rana-sylvatica/rana-tadpole/PCBs/Motherboard/KiCAD files/qw-footprints/qw-footprints/RP2040_QFN_PACKAGE.STEP

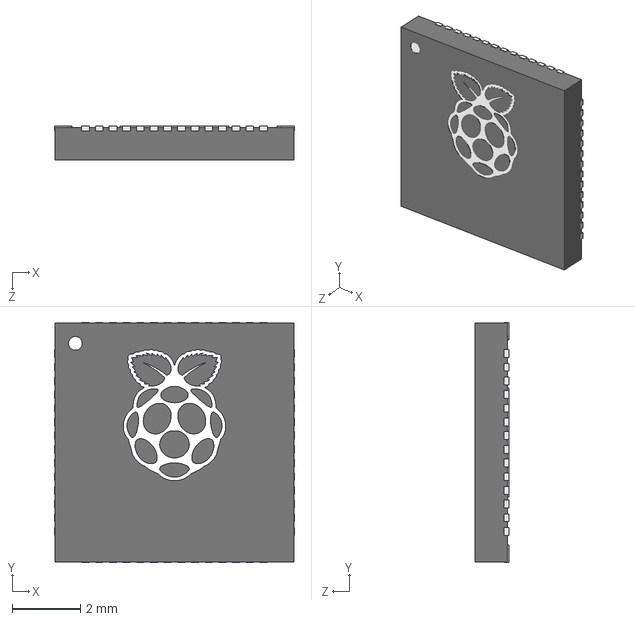
[picture p15: CAD file, 2023-10-02, an earlier design]
PCBs/Motherboard/KiCAD files/qw-footprints/qw-footprints/RP2040_QFN_PACKAGE.STEP
7.02 x 7.02 x 1.00 mm
